IRTrail/Flight-Sim-Stuff/Short Final Rudder Pedals/Printable Files/End Brackets/RR Cap.3mf

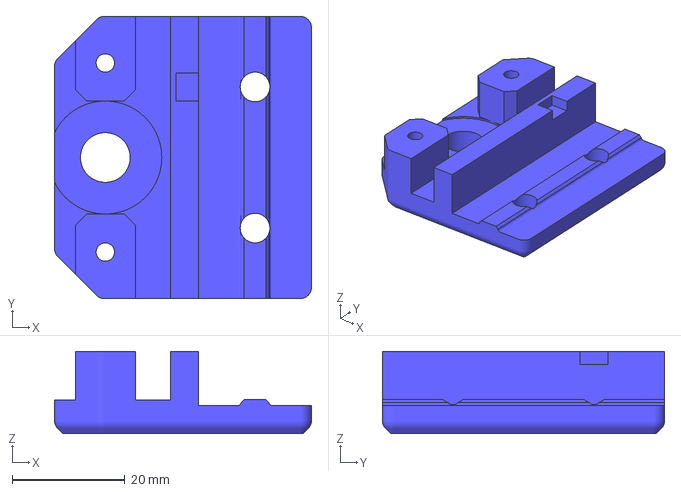
[picture p16: CAD file, 2023-03-27]
Short Final Rudder Pedals/Printable Files/End Brackets/RR Cap.3mf
45.5 x 50.0 x 14.6 mm
