IRTrail/Flight-Sim-Stuff/Short Final Rudder Pedals/Printable Files/Build Aids/400mm Width Spacer.3mf

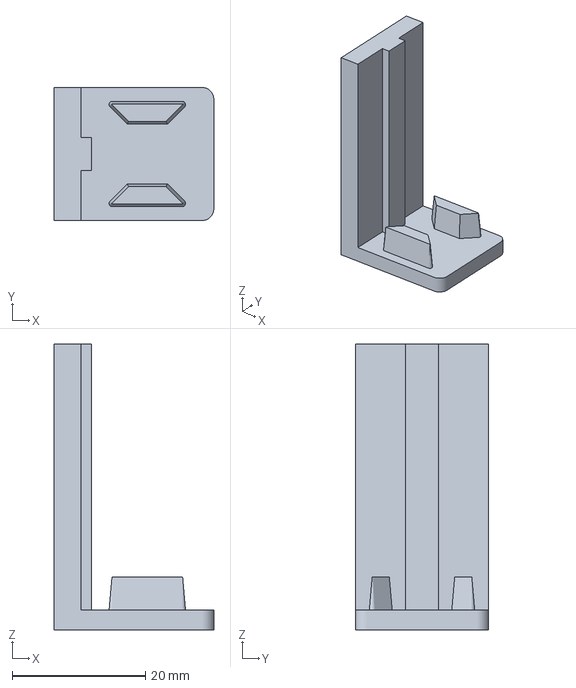
[picture p17: CAD file, 2023-03-21]
Short Final Rudder Pedals/Printable Files/Build Aids/400mm Width Spacer.3mf
24.0 x 20.0 x 43.0 mm
