IRTrail/Flight-Sim-Stuff/Short Final Rudder Pedals/Printable Files/End Brackets/RF Base.3mf

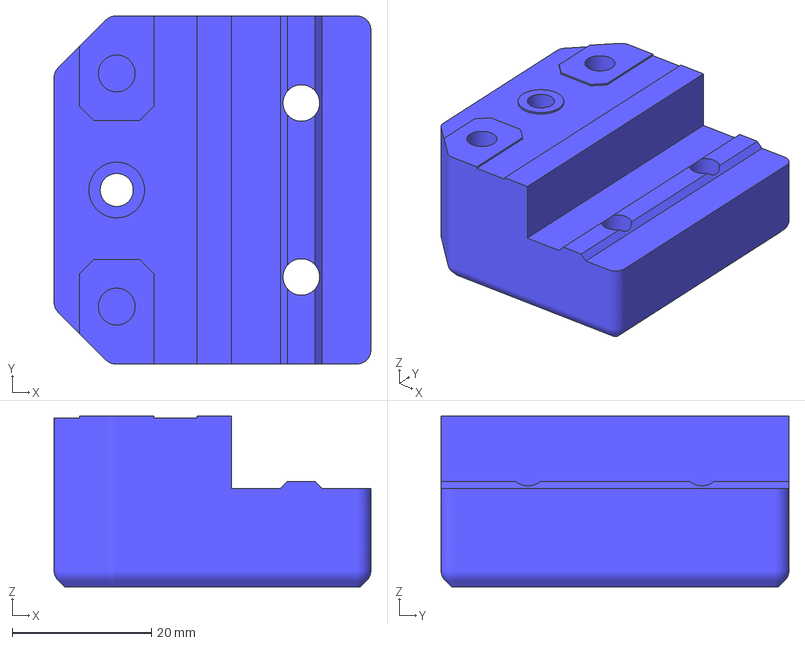
[picture p18: CAD file, 2023-03-27]
Short Final Rudder Pedals/Printable Files/End Brackets/RF Base.3mf
45.5 x 50.0 x 24.5 mm
