IRTrail/Flight-Sim-Stuff/Short Final Rudder Pedals/Printable Files/Pedals/Pedal Bushing x 4.3mf

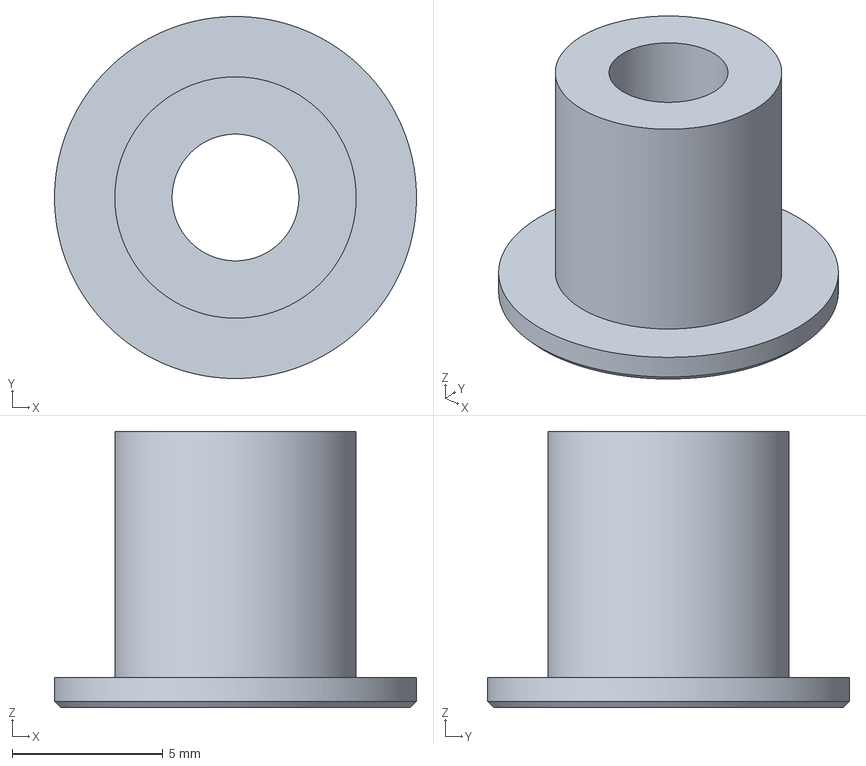
[picture p19: CAD file, 2023-03-20]
Short Final Rudder Pedals/Printable Files/Pedals/Pedal Bushing x 4.3mf
12.0 x 12.0 x 9.15 mm
