IRTrail/Flight-Sim-Stuff/Short Final Rudder Pedals/Printable Files/Build Aids/50mm Rail Spacer x 2.3mf

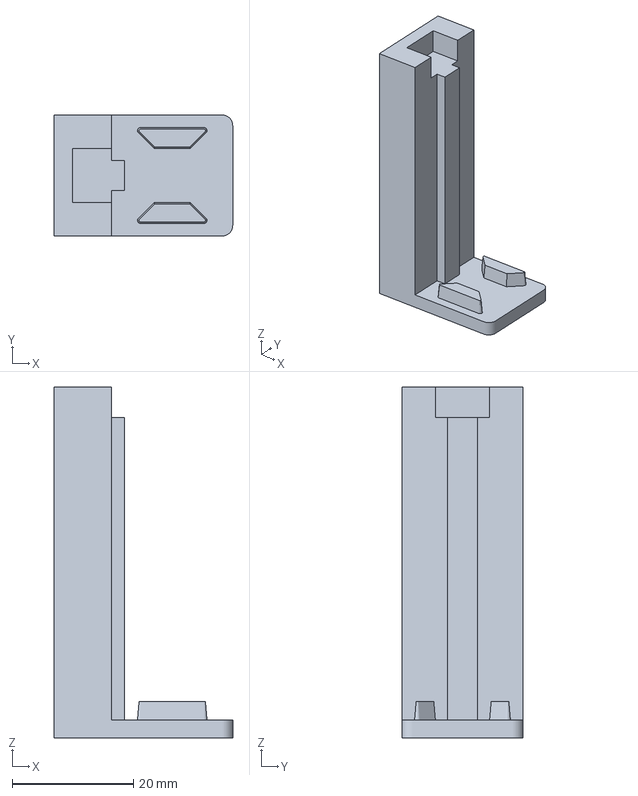
[picture p20: CAD file, 2023-03-21]
Short Final Rudder Pedals/Printable Files/Build Aids/50mm Rail Spacer x 2.3mf
29.5 x 20.0 x 58.0 mm
