IRTrail/Flight-Sim-Stuff/Short Final Rudder Pedals/Printable Files/Main Housing/Tensioner Bearing Spacer.3mf

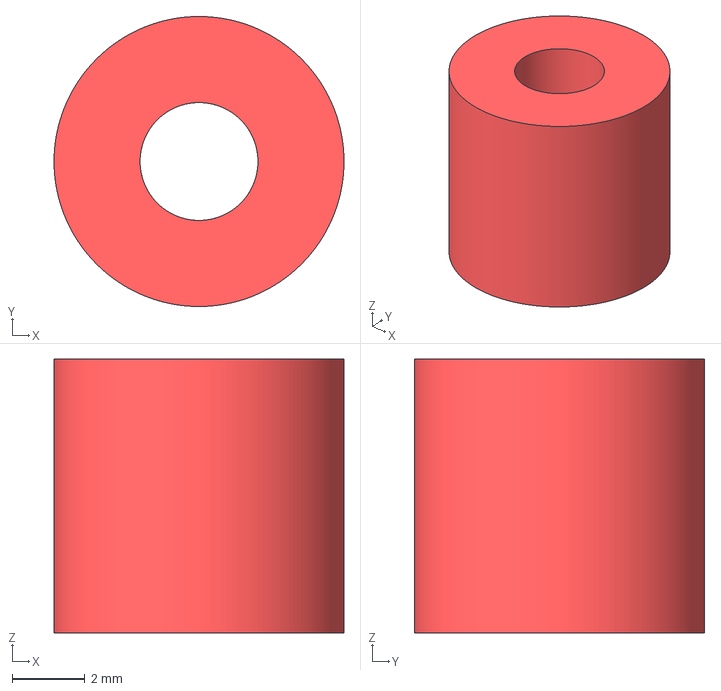
[picture p21: CAD file, 2023-03-19]
Short Final Rudder Pedals/Printable Files/Main Housing/Tensioner Bearing Spacer.3mf
8.00 x 8.00 x 7.55 mm
