IRTrail/Flight-Sim-Stuff/Short Final Rudder Pedals/Printable Files/Pedals/Pedal Pivot x 2.3mf

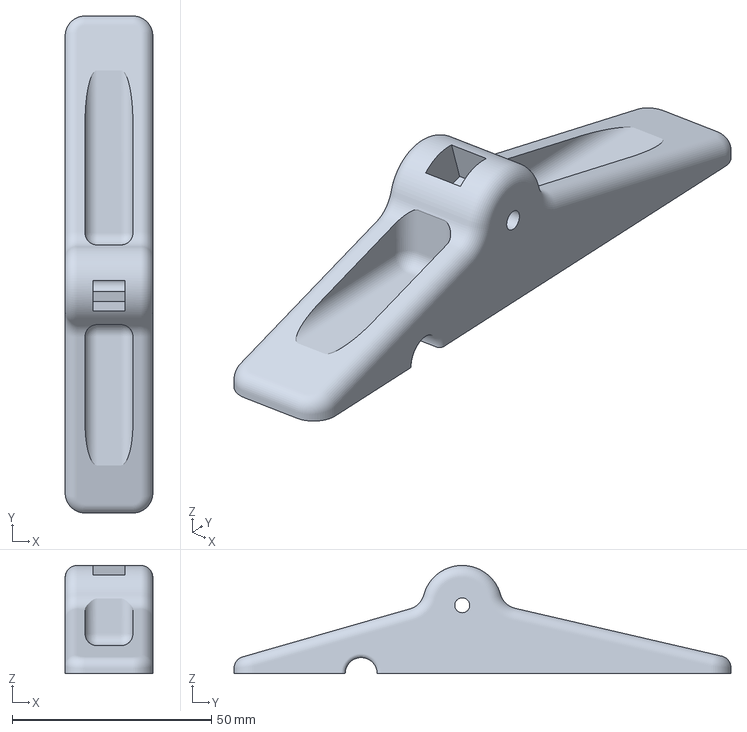
[picture p22: CAD file, 2023-03-20]
Short Final Rudder Pedals/Printable Files/Pedals/Pedal Pivot x 2.3mf
22.0 x 124.7 x 27.1 mm
