IRTrail/Flight-Sim-Stuff/Short Final Rudder Pedals/Printable Files/Build Aids/350mm Width Spacer.3mf

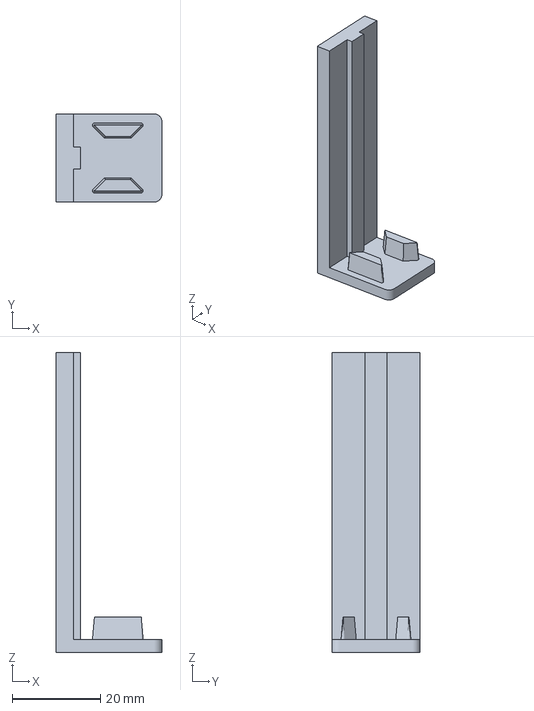
[picture p23: CAD file, 2023-03-21]
Short Final Rudder Pedals/Printable Files/Build Aids/350mm Width Spacer.3mf
24.0 x 20.0 x 68.0 mm
