IRTrail/Flight-Sim-Stuff/Short Final Rudder Pedals/Printable Files/Main Housing/Sensor Bracket.3mf

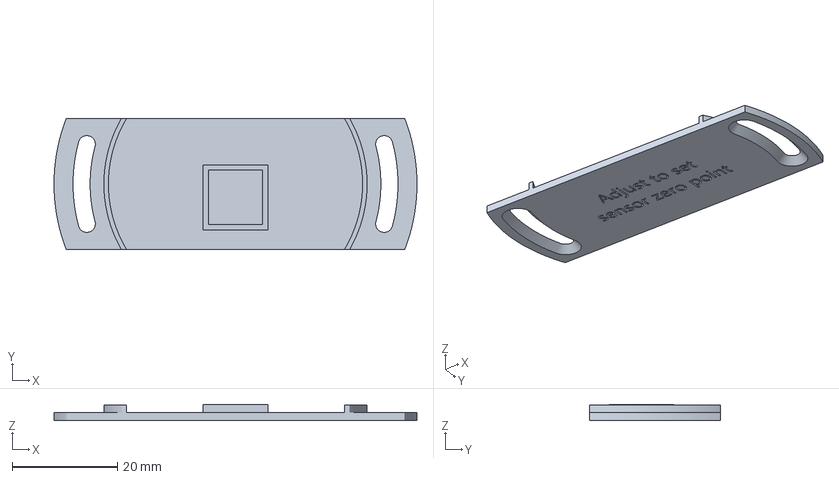
[picture p24: CAD file, 2023-03-19]
Short Final Rudder Pedals/Printable Files/Main Housing/Sensor Bracket.3mf
69.1 x 25.0 x 3.09 mm
