IRTrail/Flight-Sim-Stuff/Short Final Rudder Pedals/Printable Files/Pedals/Pedal x 2.3mf

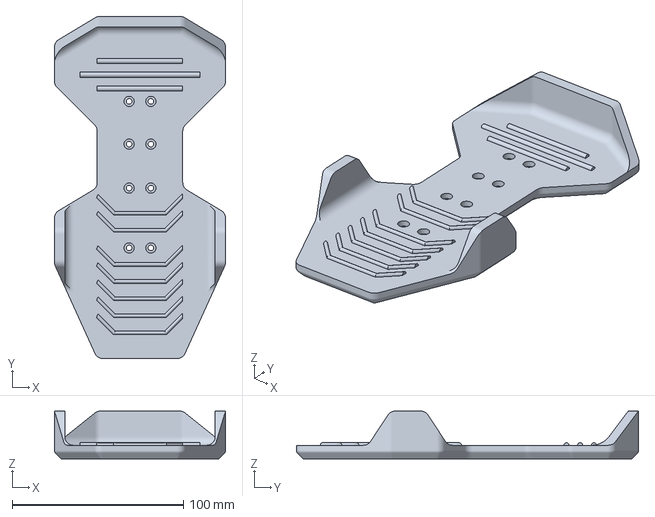
[picture p25: CAD file, 2023-03-20]
Short Final Rudder Pedals/Printable Files/Pedals/Pedal x 2.3mf
100.0 x 200.0 x 28.0 mm
