IRTrail/Flight-Sim-Stuff/Short Final Rudder Pedals/Printable Files/End Brackets/Tension Lug x2.3mf

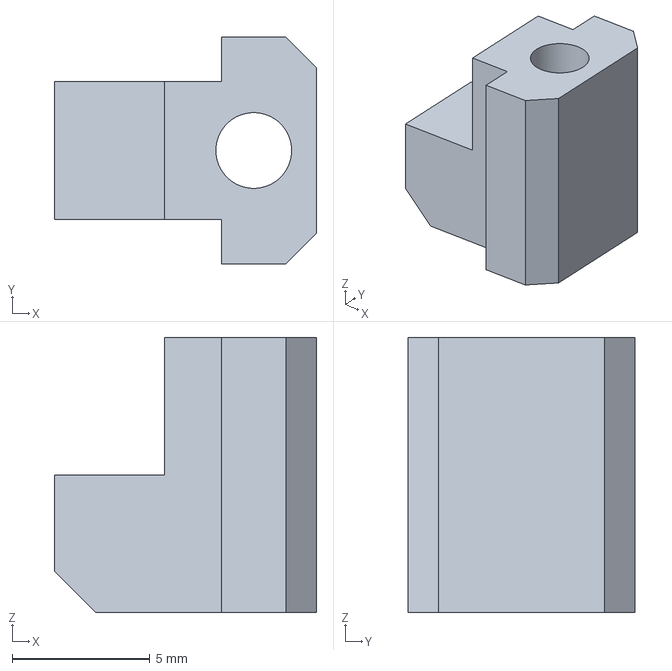
[picture p26: CAD file, 2023-03-27]
Short Final Rudder Pedals/Printable Files/End Brackets/Tension Lug x2.3mf
9.52 x 8.25 x 10.0 mm
