IRTrail/Flight-Sim-Stuff/Short Final Rudder Pedals/Printable Files/Main Housing/Tensioner pivot.3mf

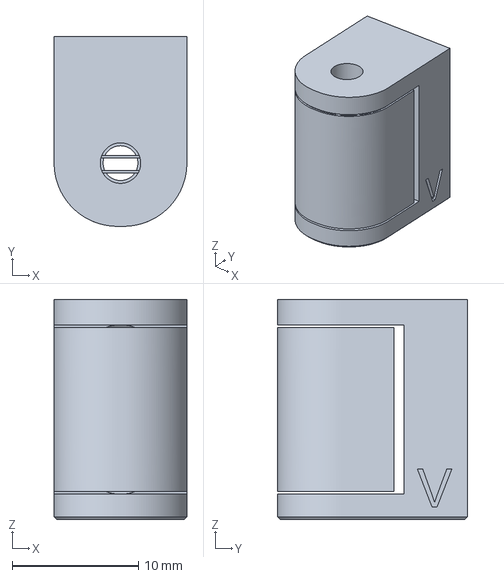
[picture p27: CAD file, 2023-03-19]
Short Final Rudder Pedals/Printable Files/Main Housing/Tensioner pivot.3mf
10.5 x 15.0 x 17.4 mm
